MATTMCCA/Thermal-Logo/B-card_rev2/img/bot.png

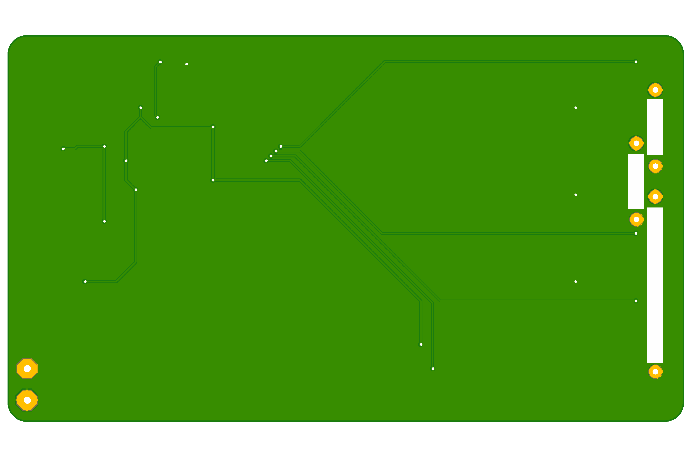
B-card_rev2/img/bot.png
