MATTMCCA/Thermal-Logo/B-card_rev2/img/rev_002 v1.png

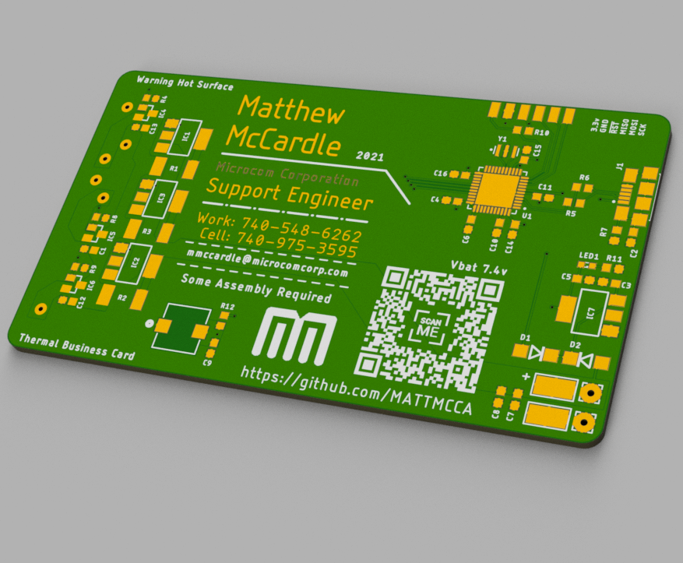
B-card_rev2/img/rev_002 v1.png
