MATTMCCA/Thermal-Logo/B-card_rev2/img/rev_002 v2.png

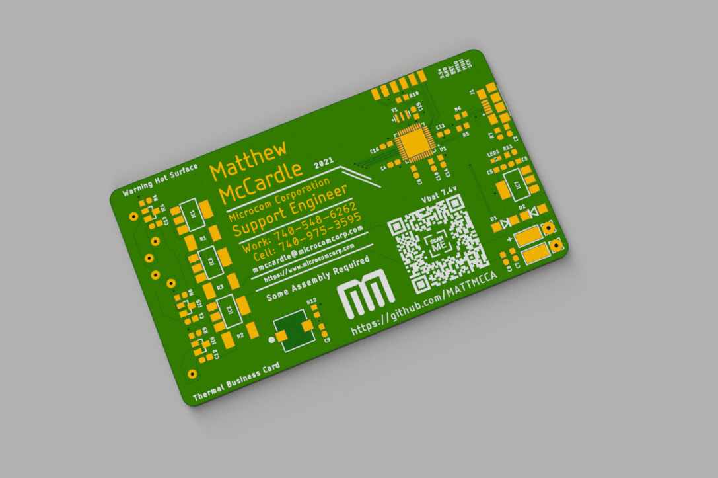
B-card_rev2/img/rev_002 v2.png
