MATTMCCA/Thermal-Logo/B-card_rev2/img/rev_002 v7.png

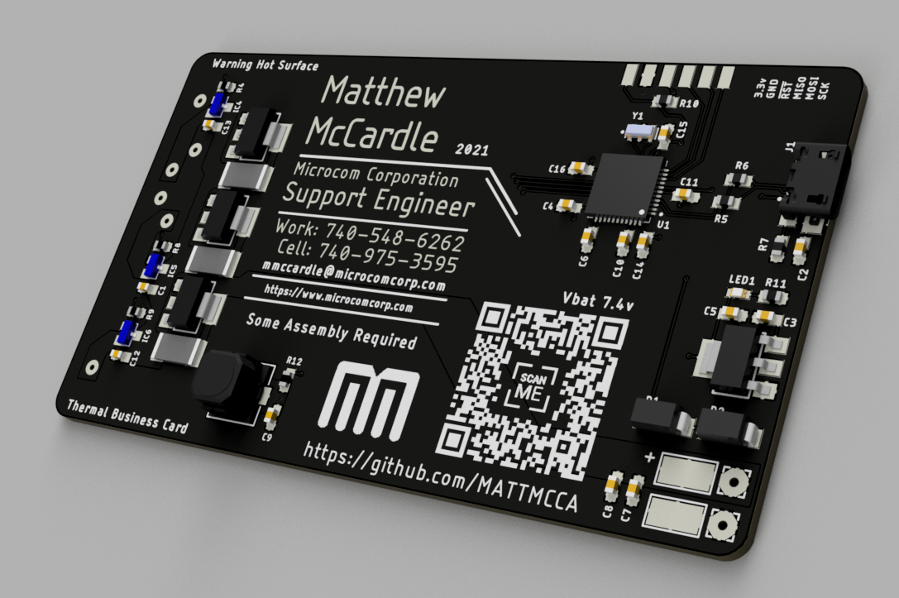
B-card_rev2/img/rev_002 v7.png
