MATTMCCA/Thermal-Logo/B-card_rev2/img/rev_002_top.png

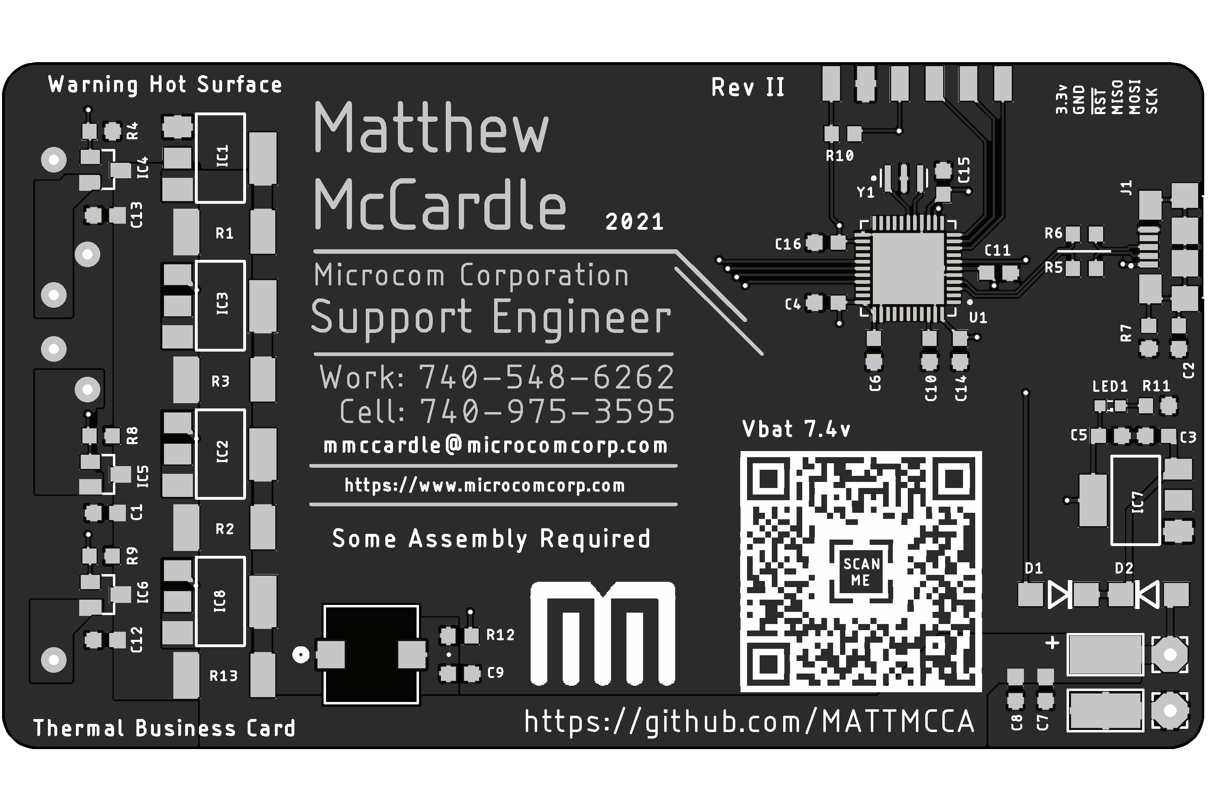
B-card_rev2/img/rev_002_top.png
