MATTMCCA/Thermal-Logo/B-card_rev2/img/top.png

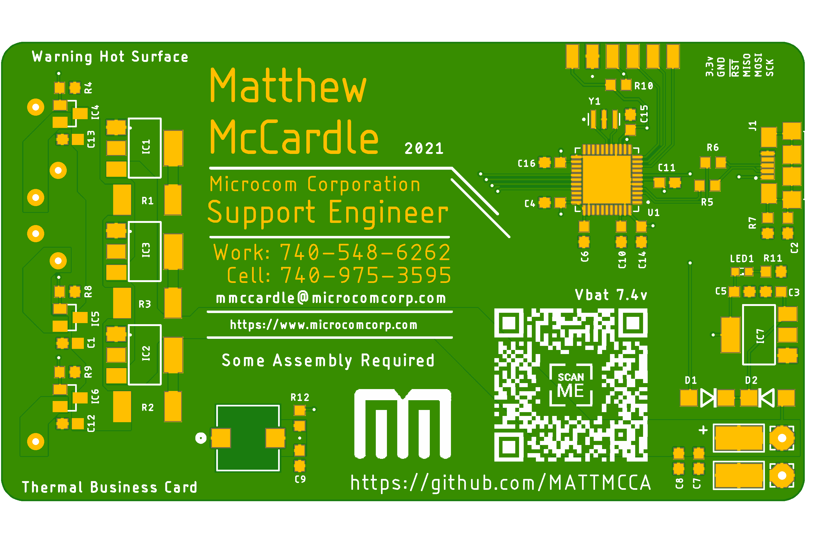
B-card_rev2/img/top.png
