MATTMCCA/Thermal-Logo/B-card_rev2/Nichrome_Thermal_Profile/001_wire.png

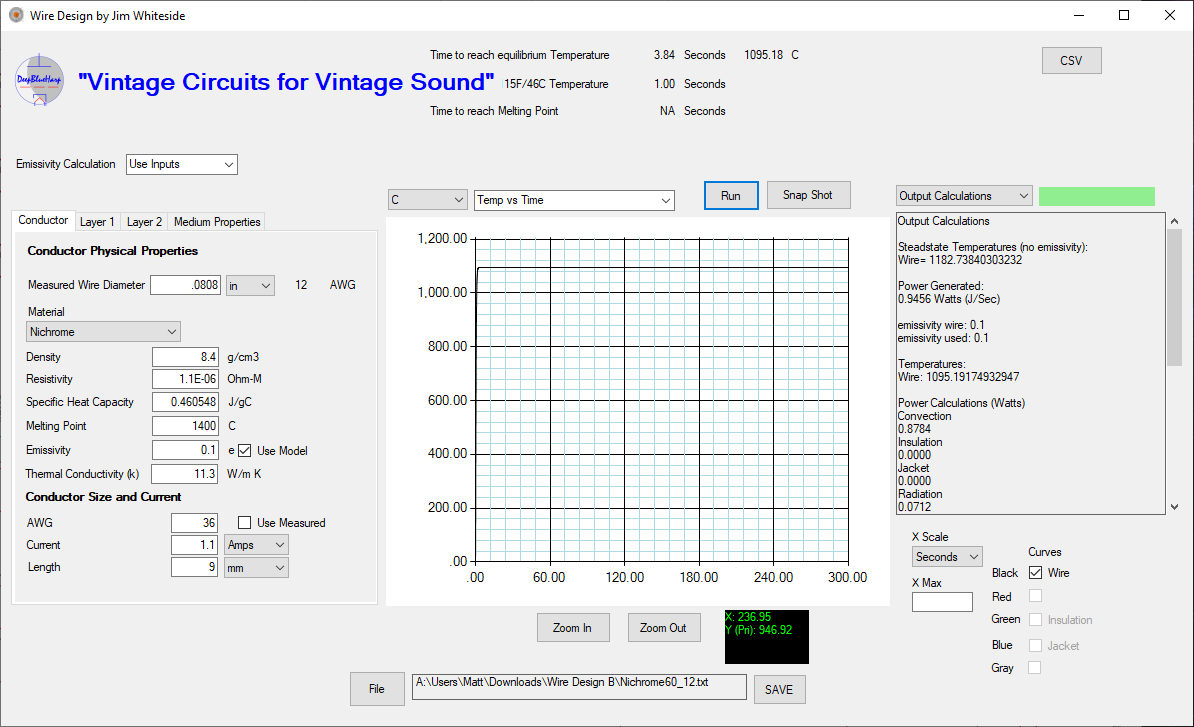
B-card_rev2/Nichrome_Thermal_Profile/001_wire.png
