MATTMCCA/Thermal-Logo/B-card_rev2/Nichrome_Thermal_Profile/002_wire.png

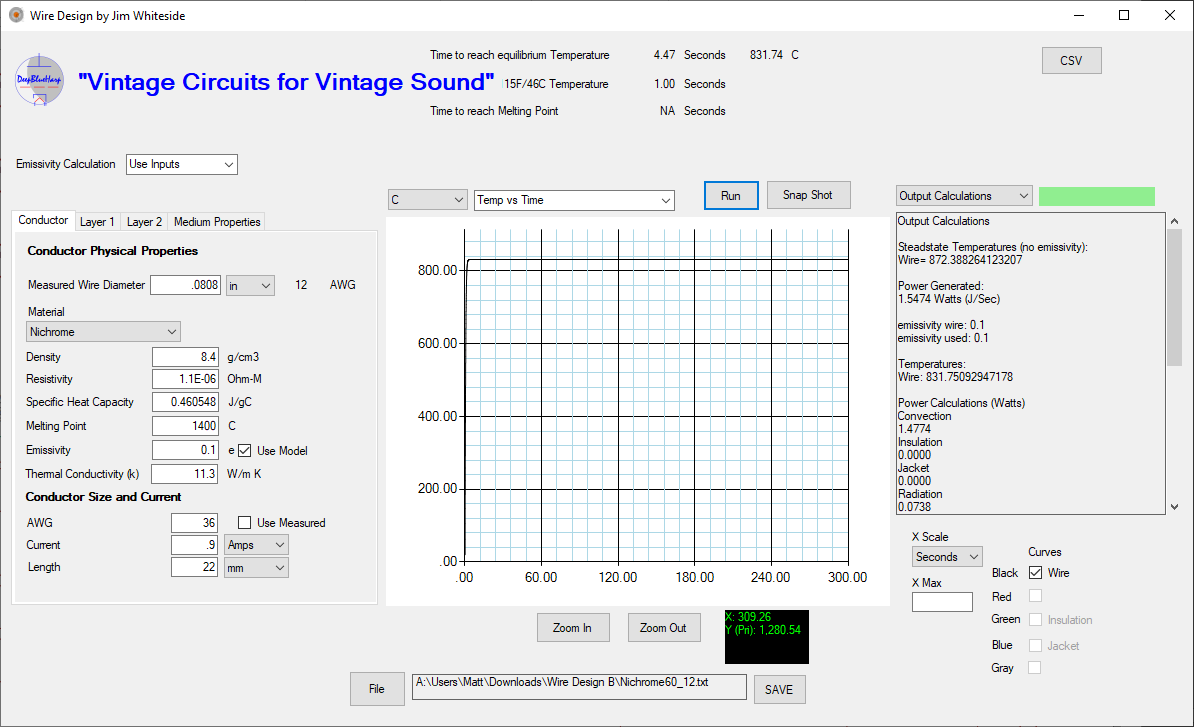
B-card_rev2/Nichrome_Thermal_Profile/002_wire.png
