MATTMCCA/Thermal-Logo/B-card_rev2/ref/logic_001.png

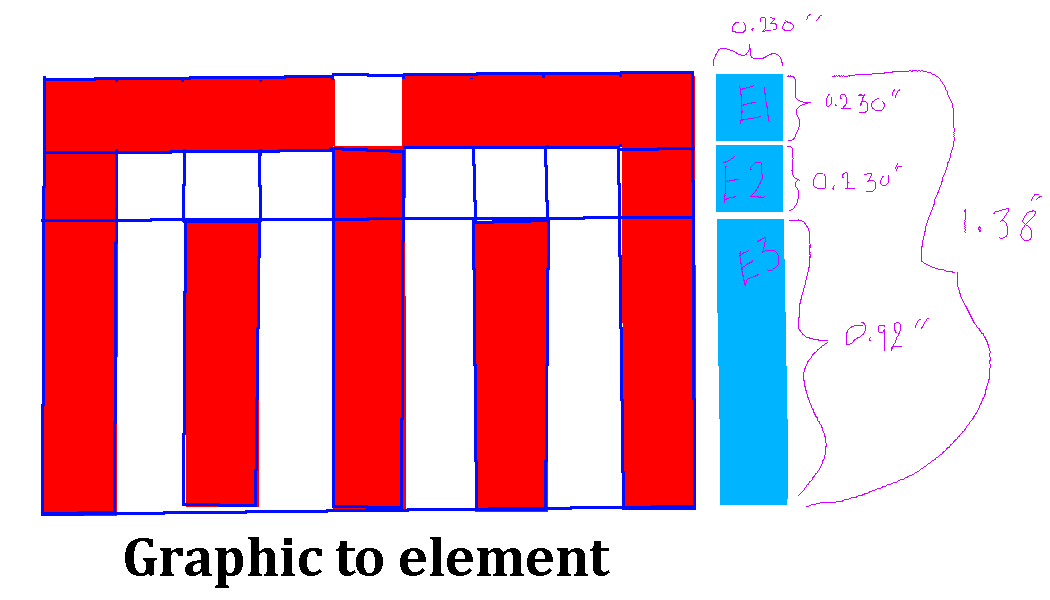
B-card_rev2/ref/logic_001.png
