MATTMCCA/Thermal-Logo/B-card_rev2/img/build_001/005.png

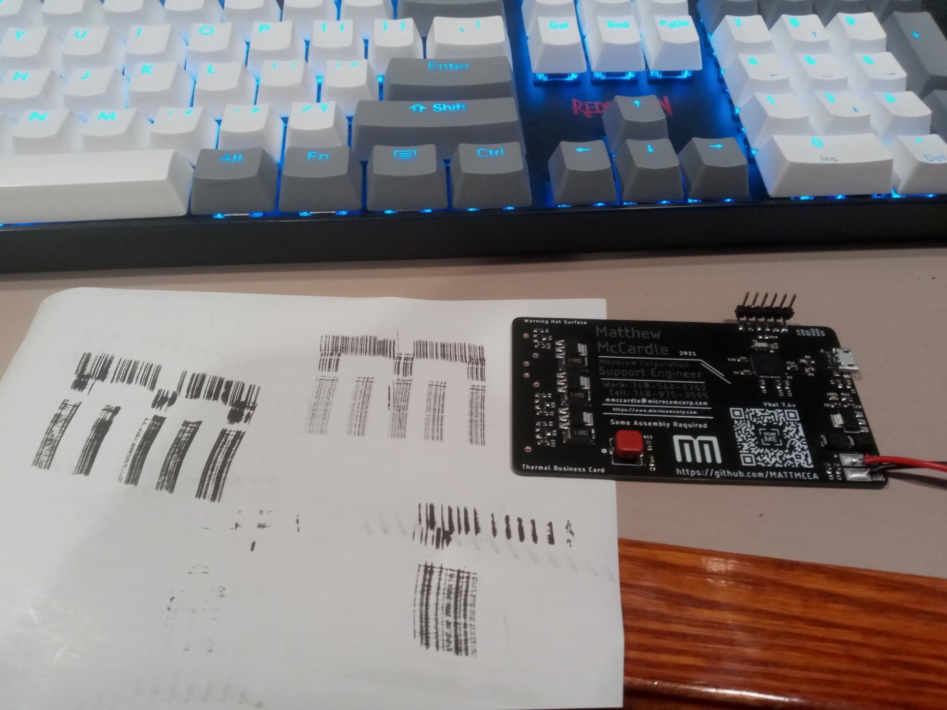
B-card_rev2/img/build_001/005.png
