MATTMCCA/Thermal-Logo/B-card_rev2/img/tests/drag_test_prelim.png

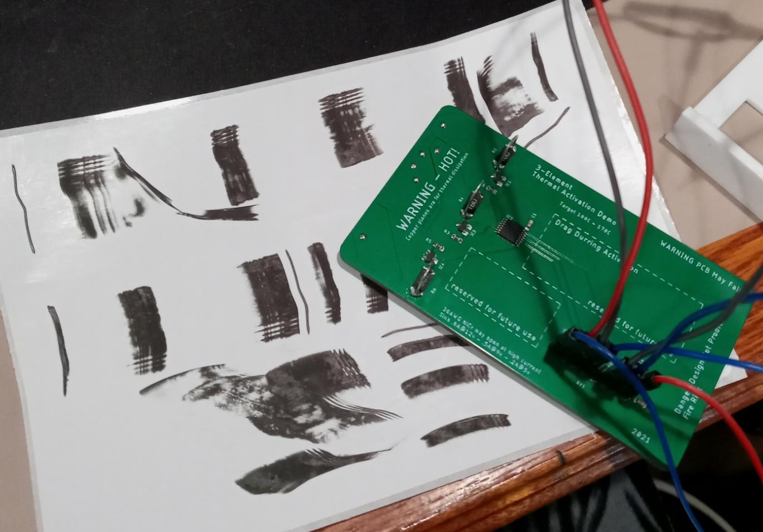
B-card_rev2/img/tests/drag_test_prelim.png
