MATTMCCA/Thermal-Logo/B-card_rev2/img/tests/pcb_002.png

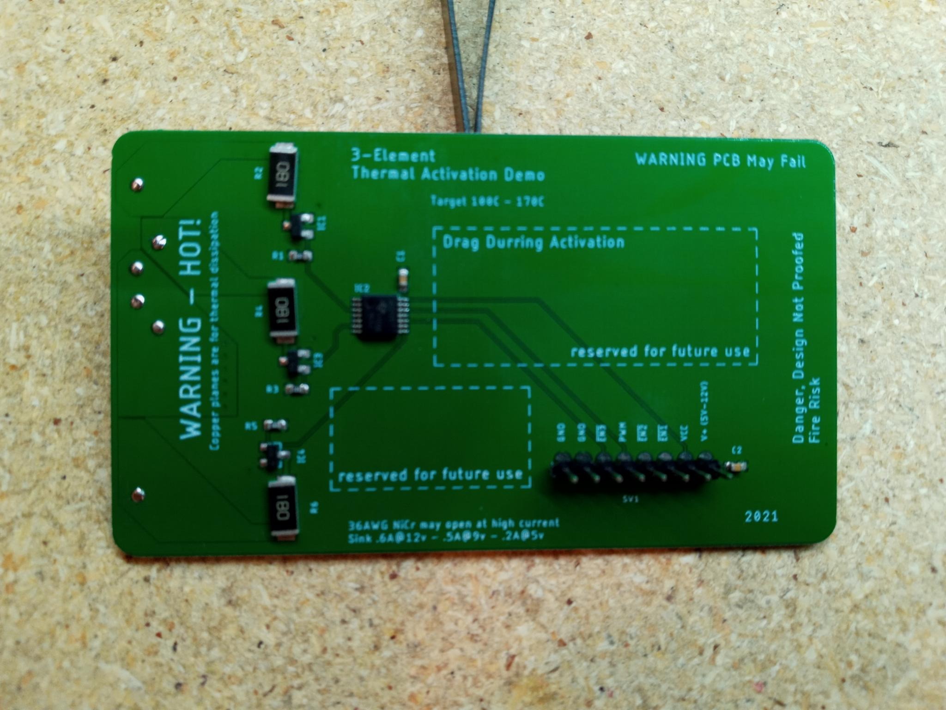
B-card_rev2/img/tests/pcb_002.png
