MATTMCCA/Thermal-Logo/B-card_rev2/img/tests/via_size.png

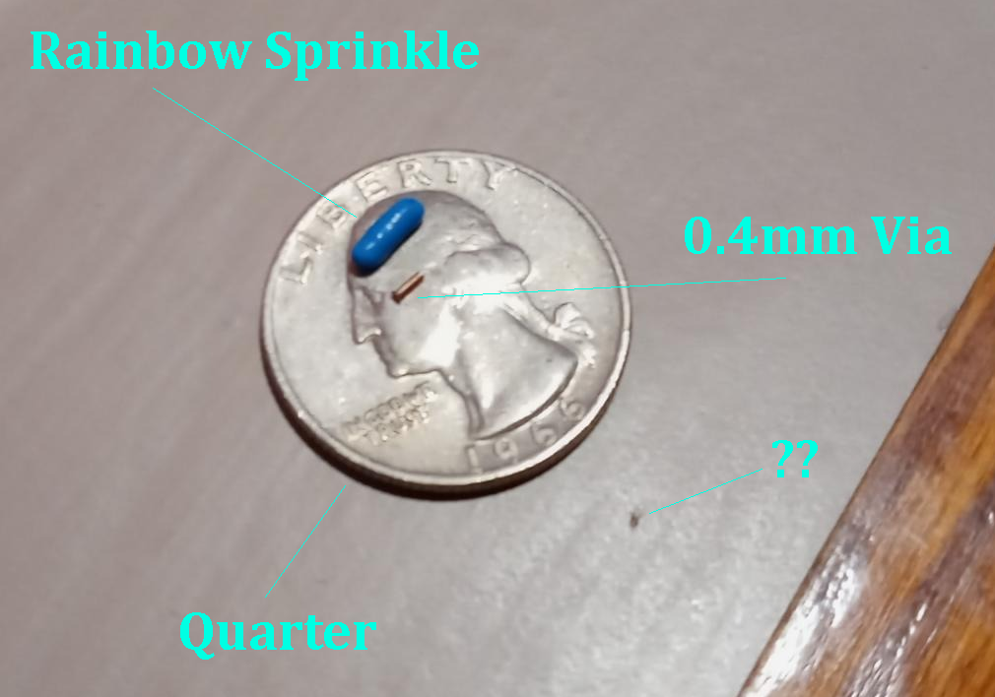
B-card_rev2/img/tests/via_size.png
