MATTMCCA/Thermal-Logo/prelim/test_temp/img/bot.png

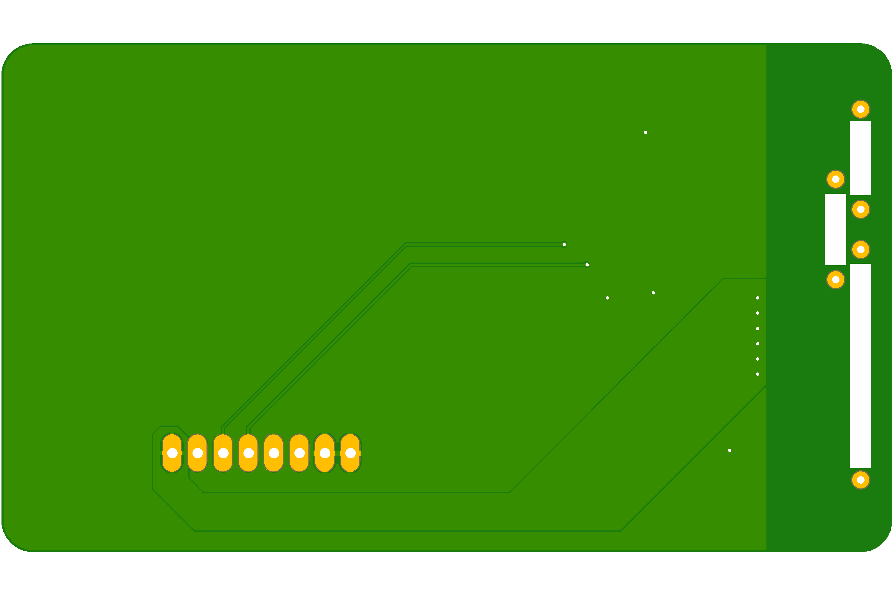
prelim/test_temp/img/bot.png
