MATTMCCA/Thermal-Logo/prelim/test_temp/img/top.png

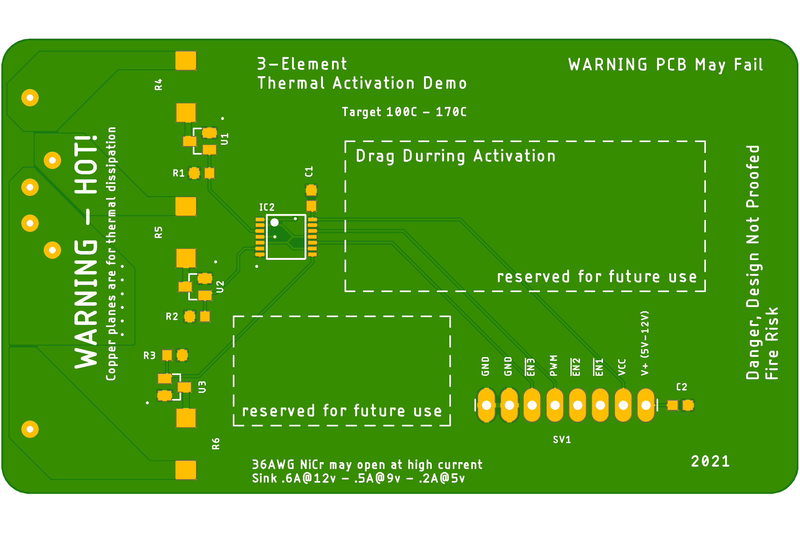
prelim/test_temp/img/top.png
